Lasthope027/Radio-station/Transmitter/Circuit .asc

C1: cap; 30pF
C2: cap; 30pF
C3: cap; 20pF
C4: cap; 100nF
C5: cap; 3.3pF
C6: cap; 10pF
C7: cap; 30pF
C8: cap; 100pF
C9: cap; 0.1ľF
C10: cap; 100n
C11: cap; 10nf
C12: cap; 3.3p
C13: cap; 100p
C14: cap; 100pF
C15: cap; 470pF
C16: cap; 33pF
C17: cap; 100nF
C18: EKMR451VSN471MR45S
C19: cap; 68p
C20: cap; 47p
C21: cap; 47p
C22: cap; 82p
C23: cap; 100n
C24: polcap; 10ľ
C25: cap; 15n
C26: cap; 0.1ľ
C27: cap; 100n
C29: cap; 470p
Cin1: cap; 10p
D1: varactor; BB910
D2: diode; 1N5819
D3: diode; 1N5819
L1: ind; 100nH
L2: ind; 220nH
L3: ind; 1ľH
L4: ind; 120nH
L5: ind; 68n
L6: ind; 100nH
L7: ind; 82n
L8: ind; 68n
L9: res; 1k
L11: ind; 47ľ
Q1: npn; BF494
Q2: npn; BF494
Q3: npn; BF494
Q4: npn; 2SC1971
R1: res; 4.7k
R2: res; 1k
R3: res; 1.5k
R4: res; 470
R5: res; 68K
R6: res; 10k
R7: res; 820
R8: res; 100k
R9: res; 4.7K
R10: res; 2.2K
R11: res; 0.1
R12: res; 1.8k
R13: res; 5.6k
R14: res; 0.1
R15: res; 1k
R16: res; 1k
R17: res; 100k
R18: res; 3.3k
R19: res; 3.3k
R20: res; 3.3k
R21: res; 10k
R22: res; 32
R23: res; 32
R24: res; 10k
Rant2: res; 66.85
Rbias: res; 47k
Rbleed1: res; 10Meg
RV1: res; 1k
V1: voltage; 12V
V3: voltage; 24V
VL1: voltage; SINE(0 3.4 15k)
VR1: voltage; SINE(0 3.4 15k)
Named nets: 0, Driveroutput, Bo, Node_A, Node_Y, Audio_Input, N_SUM, N_ATTEN_IN, N_ATTEN_OUT, N_TRIM_OUT, L, R, Audio_GND, N_PREEMP, MIC_input, N_LIMIT, Output, N_INJECT, Supply
.model BF494 NPN (IS=8e-15 BF=150 VAF=80 IKF=0.02 ISE=5e-14 NE=1.5 BR=3 NR=1 RB=4 RC=0.6 RE=0.25 CJE=3p VJE=0.75 MJE=0.33 CJC=1p VJC=0.5 MJC=0.33 TF=0.9n TR=20n)
.model BB910 D(Cjo=30p Vj=0.7 M=0.5 Rs=1.2)
.model 2SC1971 NPN IS=2e-14 BF=80 NF=1 VAF=100 IKF=2 ISE=1e-13 NE=1.4 BR=6 NR=1 RB=0.8 RC=0.2 RE=0.05 CJE=30p VJE=0.75 MJE=0.33 CJC=8p VJC=0.5 MJC=0.33 TF=0.2n TR=15n
.meas TRAN Vrms RMS V(supply) FROM 1u TO 10u
.meas tran Pout PARAM (Vrms*Vrms/67)
.tran 0 100u 50u 1n
.four 100Meg V(supply)
.meas TRAN Irms RMS I(Rant2) FROM 1u TO 10u
.meas TRAN Pout1 PARAM (Vrms*Irms)
.model 1N5819 D(Is=5e-6 Rs=0.2 N=1.05 Cjo=110p M=0.5 Vj=0.2 Bv=40 Ibv=1m Tt=0)
Trimmer(10k)
RF Processing Circuit
Antenna
Audio Interface Circuit
